ElektroBene/IR-Remote/schematics/voltage_regulator/voltage_regulator.asc

C1: cap; 0.33µ
C2: cap; 0.1µ
R1: res; 1k
U1: LT1086-5
V1: voltage; SINE(9 0.1 1k)
Named nets: 0
.tran 100m
